pdjr-wemos/MULTI001/berker-sensor-acdc/berker-sensor-acdc.sch

## KiCad design berker-sensor-acdc/berker-sensor-acdc.sch (2024-01-23)

Schematic: berker-sensor-acdc.sch

Parts:
C1: 0.1uF/275V; PANASONIC_100nF_275VAC
C2: 100uF/25V; CP_Radial_D5.0mm_P2.00mm
F1: 10mA SB; BEL_MRT_SERIES
J1, J2: Conn_01x01; KYOCERA_POKEHOME_1P
J3: Conn_01x02; PinHeader_1x02_P2.54mm_Vertical
U1: VTX-214-001-105; VTX214001103
